lambdakb/keyboard-lk16c/output/pcb/img/lk16c-pcb-bottom.png

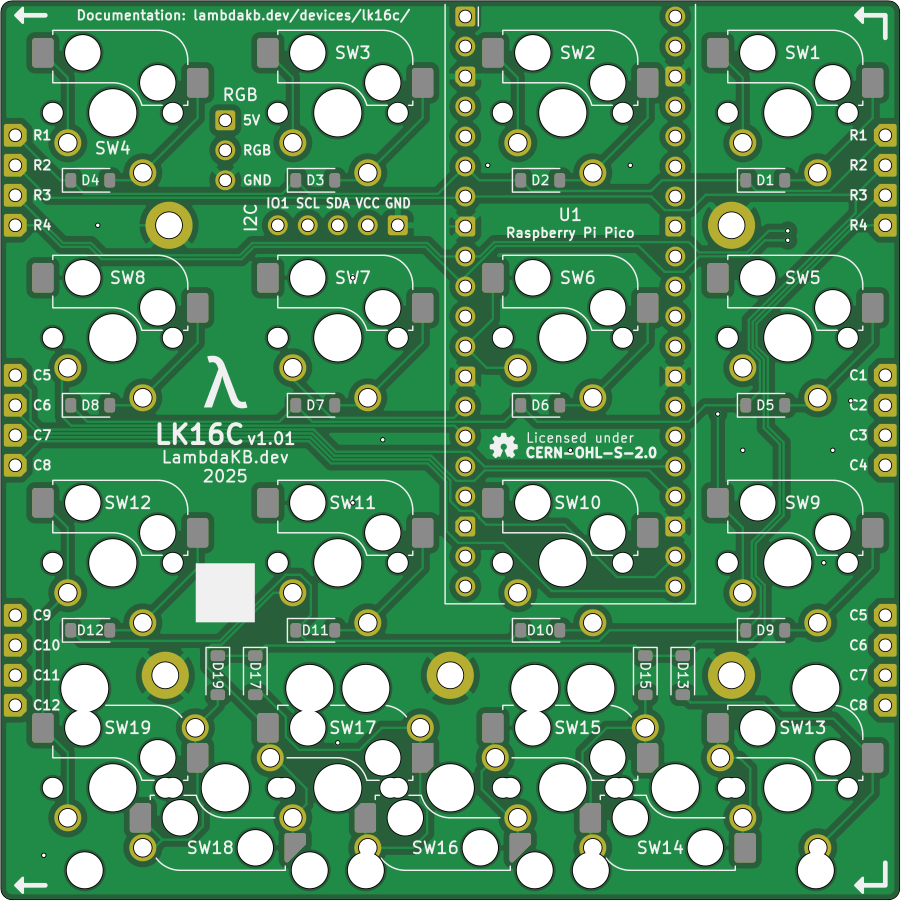
output/pcb/img/lk16c-pcb-bottom.png
