lambdakb/keyboard-lk16c/output/pcb/img/lk16c-pcb-top.png

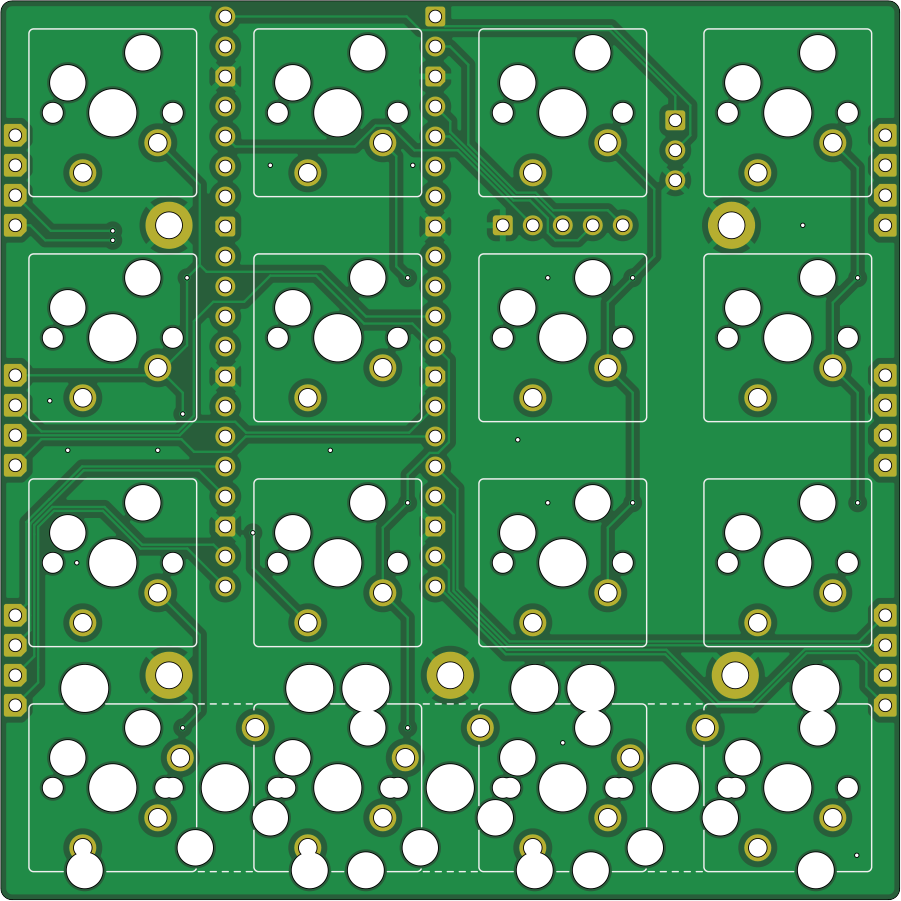
output/pcb/img/lk16c-pcb-top.png
