lambdakb/keyboard-lk16c/output/plate/img/lk16c-plate_2space-bottom.png

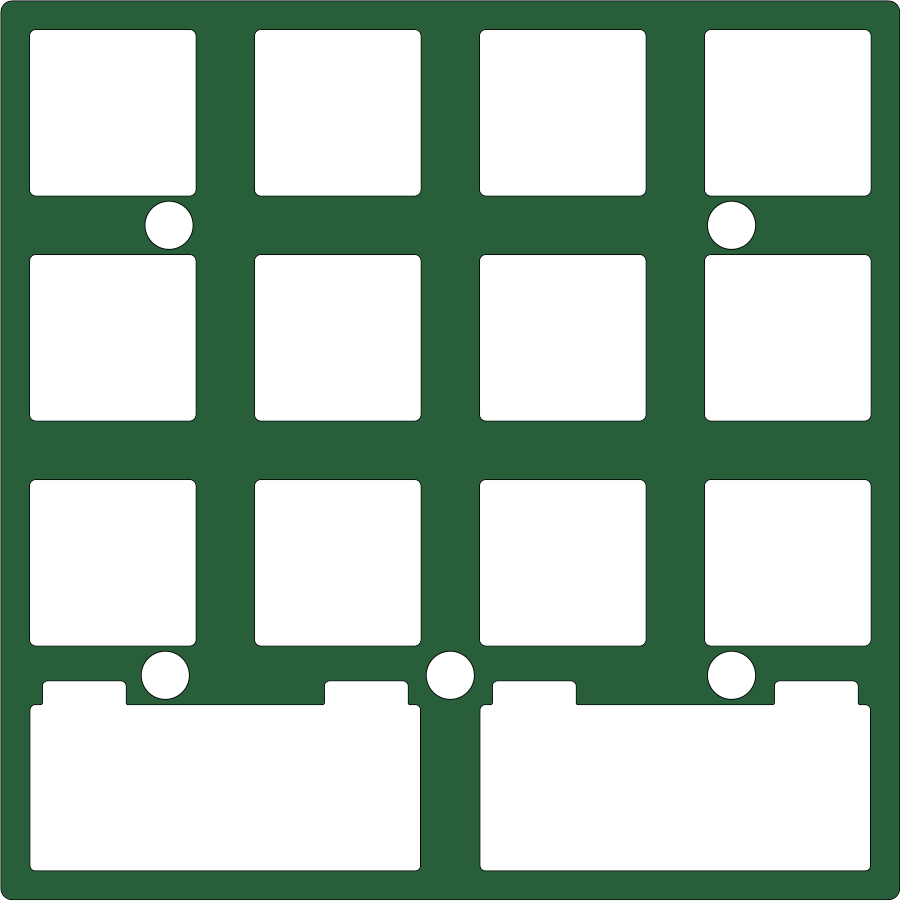
output/plate/img/lk16c-plate_2space-bottom.png
